TinyCircuits/TinyCircuits-TinyShield-7Segment-ASD2421/images/ASD2421-R-N-Tutorial-Image-01.2.png

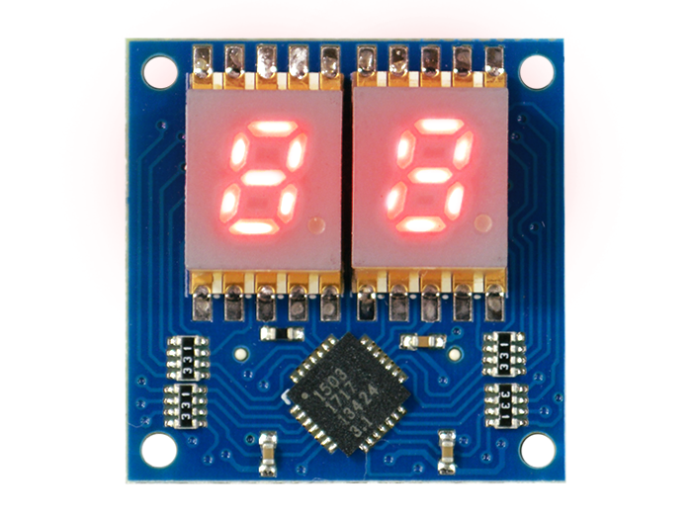
images/ASD2421-R-N-Tutorial-Image-01.2.png
